RileyMcCarthy/MaD-Tensile-Tester/Firmware/MaD_Firmware/src/Motion.cpp

#include "Motion.h"
#include <propeller.h>
extern Motion_Cog motionCog;

/**
 * @brief The motion cog function that handles reading the force gauge and controlling the servo withen state machine restriction
 * 
 * @param par ignore this parameter, used for cog_run()
 */
void runMotion(void *par)
{
    //Start state machine
    /* if (!RunStateMachine())
    {
        //state machine failed to run
    }*/

    //MachineState.selfCheckParameters.chargePumpOK = true; //motion cog started up successfully, enable charge pump

    ForceGauge forceGauge;
    ForceGauge_begin(&forceGauge, 15, 16);
    /* if (ForceGauge_begin(&forceGauge, 15, 16) == SUCCESS)
    {
        MachineState.machineCheckParameters.forceGaugeResponding = true;
    }*/

    DYN4 dyn4;
    dyn4_begin(&dyn4, 14, 12, 0x03);
    /* if (dyn4_begin(&dyn4, 14, 12, 0x03) == SUCCESS)
    {
        MachineState.machineCheckParameters.dyn4Responding = true;
    }*/
    dyn4_send_command(&dyn4, 0x0c, 1000);
    int startCNT = CNT;
    for (;;)
    {
        motionCog.time = (CNT - startCNT) / CLKFREQ;
        motionCog.position = dyn4.encoder.POS[0];
        motionCog.force = forceGauge.force;
        //char data[50];
        // sprintf(data, "%d,%d,%d\n", motionCog.time, motionCog.position, motionCog.force);
        // count++;
        waitcnt(CNT + CLKFREQ / 1000);
    }

    // sd.Close();
}
